KhoiVuKha/SingleTouch/SourceCode/src/USB_SRC/elog.c

/*
 * Log module
 *
 * Provide logging output via the serial port
 */
#include "clock.h"
#include "elog.h"

void elog_start(const char *name, uint16_t line)
{
    //printf("%08x:%s:%d ", (unsigned int) clock_now(), name, line);
}
